ZipCPU/videozip/rtl/wbi2c/wbi2cslave.v

////////////////////////////////////////////////////////////////////////////////
//
// Filename:	rtl/wbi2c/wbi2cslave.v
// {{{
// Project:	VideoZip, a ZipCPU SoC supporting video functionality
//
// Purpose:	To create an I2C Slave that can be accessed via a wishbone bus.
//
//	This core works by creating a dual-port 128-byte memory, that can be
//	written to via either 1) the I2C bus which it acts as a slave upon,
//	2) an AXI slave port, or 3) the wishbone bus it is connected to.  The
//	128 bytes of slave memory may be referenced, read, and written to via
//	either of the I2C or WB busses.
//
//	The AXI slave port was added as an after thought to allow forwarding
//	of a read only I2C port (such as EDID info from a downstream monitor).
//
// Creator:	Dan Gisselquist, Ph.D.
//		Gisselquist Technology, LLC
//
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
// This program is distributed in the hope that it will be useful, but WITHOUT
// ANY WARRANTY; without even the implied warranty of MERCHANTIBILITY or
// FITNESS FOR A PARTICULAR PURPOSE.  See the GNU General Public License
// for more details.
//
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
////////////////////////////////////////////////////////////////////////////////
//
`default_nettype	none
// }}}
module	wbi2cslave #(
		// {{{
		// Verilator lint_off UNUSED
		parameter	INITIAL_MEM = "",
		// Verilator lint_on  UNUSED
		parameter [0:0]	WB_READ_ONLY  = 1'b0,
		parameter [0:0]	I2C_READ_ONLY = 1'b0,
		parameter [0:0]	AXIS_SUPPORT  = 1'b1,
		parameter [6:0]	SLAVE_ADDRESS = 7'h50,
		parameter	MEM_ADDR_BITS = 8
		// }}}
	) (
		// {{{
		input	wire		i_clk, i_reset,
		// Bus access
		// {{{
		input	wire		i_wb_cyc, i_wb_stb, i_wb_we,
		input	wire	[(MEM_ADDR_BITS-3):0]	i_wb_addr,
		input	wire	[31:0]	i_wb_data,
		input	wire	[3:0]	i_wb_sel,
		output	wire		o_wb_stall,
		output	reg		o_wb_ack,
		output	reg	[31:0]	o_wb_data,
		// }}}
		// AXI Stream access, for data from I2C
		// {{{
		input	wire		s_valid,
		output	wire		s_ready,
		input	wire	[7:0]	s_data,
		input	wire		s_last,
		// }}}
		// Actual I2C interaction
		// {{{
		input	wire		i_i2c_scl, i_i2c_sda,
		output	reg		o_i2c_scl, o_i2c_sda,
		// }}}
		output	wire	[31:0]	o_dbg
		// }}}
	);

	// Local declarations
	// {{{
	localparam [0:0] READ_ONLY = WB_READ_ONLY && I2C_READ_ONLY
							&& !AXIS_SUPPORT;

	localparam [2:0]	I2CIDLE	 = 3'h0,
				I2CSTART = 3'h1,
				I2CADDR	 = 3'h2,
				I2CSACK	 = 3'h3,// Slave ack's (that's us),
				I2CRX	 = 3'h4,// Slave receive's (that's us)
				I2CMACK	 = 3'h5,// Master acks's
				I2CTX	 = 3'h6,// Slave transmits
				I2CILLEGAL= 3'h7;

	localparam	[1:0]	BUS_IDLE = 2'b00,
				BUS_READ = 2'b01,
				BUS_SEND = 2'b10;

	reg	[31:0]	mem	[0:((1<<(MEM_ADDR_BITS-2))-1)];
	reg	[4:0]	wr_stb;
	reg	[7:0]	i2c_addr;
	wire	[7:0]	wr_data;

	reg	[3:0]	r_we;
	reg	[31:0]	r_data;
	reg	[(MEM_ADDR_BITS-3):0]	r_addr;

	reg	[(2*PL-1):0]	i2c_pipe;
	reg	last_scl, last_sda;
	// Current values are at the edge of the synchronizer
	wire	this_scl   = i2c_pipe[(2*PL-1)];
	wire	this_sda   = i2c_pipe[(2*PL-2)];

	// This allows us to notice edges
	wire	i2c_posedge= (!last_scl)&&( this_scl);
	wire	i2c_negedge= ( last_scl)&&(!this_scl);
	wire	i2c_start  = ( last_scl)&&( this_scl)&&( last_sda)&&(!this_sda);
	wire	i2c_stop   = ( last_scl)&&( this_scl)&&(!last_sda)&&( this_sda);

	reg	[2:0]	i2c_state;
	reg	[7:0]	dreg, oreg, rd_val, i2c_rx_byte;
	wire	[7:0]	i2c_tx_byte;
	reg	[2:0]	dbits;
	reg		slave_tx_rx_n, i2c_slave_ack, i2c_rx_stb, i2c_tx_stb;

	reg	[1:0]	bus_state;
	reg		go_bus_idle, wr_complete,
			bus_rd_stb, bus_wr_stb;
	reg	[2:0]	wr_pipe;
	reg	[31:0]	pipe_mem;
	reg	[1:0]	pipe_sel;
	reg	r_trigger;

	wire	[MEM_ADDR_BITS-1:0]	axis_addr;
	//

`ifndef	VERILATOR
	initial begin
		if (INITIAL_MEM != "")
			$readmemh(INITIAL_MEM, mem);
	end
`endif
	// }}}
	////////////////////////////////////////////////////////////////////////
	//
	// Wishbone interactions: Read/write set memory
	// {{{
	////////////////////////////////////////////////////////////////////////
	//
	//

	// r_data, r_addr, r_we
	// {{{
	initial	r_we = 4'h0;
	always @(posedge i_clk)
	begin
		if (!READ_ONLY)
		begin
			// Accept new data from one of three sources:
			//  1. An I2C write from the I2C master
			//	(Assuming the device can be adjusted via I2C)
			//  2. A write from the AXI stream slave port
			//  3. A WB write
			//	(Assuming the device can be adjusted via WB)
			// Writes require two clocks: one for the arbitration
			// below, and a second one to actually write the data
			// to memory.
			if ((!I2C_READ_ONLY)&&(wr_stb[4]))
			begin
				r_we <= wr_stb[3:0];
				r_addr <= i2c_addr[MEM_ADDR_BITS-1:2];
				r_data <= {(4){wr_data}};
			end else if (AXIS_SUPPORT && s_valid)
			begin
				r_we <= { 2'b00, axis_addr[1:0] };
				r_addr <= axis_addr[MEM_ADDR_BITS-1:2];
				r_data <= {(4){s_data}};
			end else if ((!WB_READ_ONLY)&&(i_wb_stb)&&(i_wb_we))
			begin
				r_we <= i_wb_sel;
				r_addr <= i_wb_addr;
				r_data <= i_wb_data;
			end
		end else
			r_we <= 4'h0;

		if (i_reset)
			r_we <= 4'h0;
	end
	// }}}

	// o_wb_data: Read from memory
	// {{{
	always @(posedge i_clk)
		o_wb_data <= mem[ i_wb_addr[(MEM_ADDR_BITS-3):0] ];
	// }}}

	// o_wb_ack, o_wb_stall
	// {{{
	initial	o_wb_ack = 1'b0;
	always @(posedge i_clk)
		o_wb_ack <= (i_wb_stb)&&(!o_wb_stall);

	// Stall on any write, when another source is also attempting to write
	//   to memory at the same time.
	assign	o_wb_stall = i_wb_we && ((!I2C_READ_ONLY && wr_stb[4])
						|| (AXIS_SUPPORT && s_valid));
	// }}}
	// }}}
	////////////////////////////////////////////////////////////////////////
	//
	// AXI Stream incoming data
	// {{{
	////////////////////////////////////////////////////////////////////////
	//
	//

	// AXI stream data can be used to set the memory of this I2C slave.
	// Writes will set one byte of memory at a time, and writes with TLAST
	// set will reset the address back to the beginning.

	generate if (AXIS_SUPPORT)
	begin : GEN_AXIS_ADDR
		reg	[MEM_ADDR_BITS-1:0]	r_axis_addr;

		initial	r_axis_addr = 0;
		always @(posedge i_clk)
		if (i_reset)
			r_axis_addr <= 0;
		else if (s_valid && s_ready)
		begin
			if (s_last)
				r_axis_addr <= 0;
			else
				r_axis_addr <= axis_addr + 1;
		end

		assign	axis_addr = r_axis_addr;

	end else begin : NO_AXIS_ADDR_SUPPORT
		assign	axis_addr = 0;
	end endgenerate

	assign	s_ready = (!AXIS_SUPPORT || I2C_READ_ONLY || !wr_stb[4]);

	// }}}
	////////////////////////////////////////////////////////////////////////
	//
	// Write to memory
	// {{{
	always @(posedge i_clk)
	if (!READ_ONLY)
	begin
		if (r_we[3])
			mem[r_addr][31:24] <= r_data[31:24];
		if (r_we[2])
			mem[r_addr][23:16] <= r_data[23:16];
		if (r_we[1])
			mem[r_addr][15: 8] <= r_data[15: 8];
		if (r_we[0])
			mem[r_addr][ 7: 0] <= r_data[ 7: 0];
	end
	// }}}
	////////////////////////////////////////////////////////////////////////
	//
	// I2C Controller
	// {{{
	////////////////////////////////////////////////////////////////////////
	//
	//


	//
	//
	// Okay, that builds our memory, and gives us access to the bus.
	// Now ... let's build the I2C slave portion to interact over that bus
	//
	//

	// 2FF Synchronizer
	localparam	PL=2;
	always @(posedge i_clk)
		i2c_pipe <= { i2c_pipe[(2*PL-3):0], i_i2c_scl, i_i2c_sda };

	// Capture the last values
	always @(posedge i_clk)
	begin
		last_scl <= i2c_pipe[(2*PL-1)];
		last_sda <= i2c_pipe[(2*PL-2)];
	end

	// i2c_state, o_i2c_scl, o_i2c_sda, i2c_slave_ack, i2c_*x_stb,dreg,oreg
	// {{{
	initial	i2c_state = I2CIDLE;
	initial	o_i2c_scl = 1'b1;
	initial	o_i2c_sda = 1'b1;
	initial	i2c_slave_ack  = 1'b1;
	always	@(posedge i_clk)
	begin
		// Default is to do nothing with the output ports.  A 1'b1 does
		// that.
		o_i2c_scl <= 1'b1;
		o_i2c_sda <= 1'b1;
		i2c_tx_stb <= 1'b0;
		i2c_rx_stb <= 1'b0;
		if (i2c_posedge)
			dreg  <= { dreg[6:0], this_sda };
		if (i2c_negedge)
			oreg  <= { oreg[6:0], oreg[0] };
		case(i2c_state)
		I2CIDLE: begin
			// {{{
			dbits <= 0;
			if (i2c_start)
				i2c_state <= I2CSTART;
			end
			// }}}
		I2CSTART: begin
			// {{{
				dbits <= 0;
				if (i2c_negedge)
					i2c_state <= I2CADDR;
			end
			// }}}
		I2CADDR: begin
			// {{{
				if (i2c_negedge)
					dbits <= dbits + 1'b1;
				if ((i2c_negedge)&&(dbits == 3'h7))
				begin
					slave_tx_rx_n <= dreg[0];
					if (dreg[7:1] == SLAVE_ADDRESS)
					begin
						i2c_state <= I2CSACK;
						i2c_slave_ack <= 1'b0;
					end else begin
						// Ignore this, its not for
						// me.
						i2c_state <= I2CILLEGAL;
						i2c_slave_ack <= 1'b1;
					end
				end
			end
			// }}}
		I2CSACK: begin
			// {{{
				dbits <= 3'h0;
				// NACK anything outside of our address range
				o_i2c_sda <= i2c_slave_ack;
				oreg <= rd_val;
				if (i2c_negedge)
				begin
					i2c_state <= (slave_tx_rx_n)? I2CTX:I2CRX;
					oreg <= i2c_tx_byte;
				end
			end
			// }}}
		I2CRX: begin	// Slave reads from the bus
			// {{{
				//
				// First byte received is always the memory
				// address.
				//
				if (i2c_negedge)
					dbits <= dbits + 1'b1;
				if ((i2c_negedge)&&(dbits == 3'h7))
				begin
					i2c_rx_byte <= dreg;
					i2c_rx_stb  <= 1'b1;
					i2c_state <= I2CSACK;
				end
			end
			// }}}
		I2CTX: begin	// Slave transmits
			// {{{
				// Read from the slave (that's us)
				if (i2c_negedge)
					dbits <= dbits + 1'b1;
				if ((i2c_negedge)&&(dbits == 3'h7))
				begin
					i2c_tx_stb <= 1'b1;
					i2c_state <= I2CMACK;
				end
				o_i2c_sda <= oreg[7];
			end
			// }}}
		I2CMACK: begin
			// {{{
				dbits <= 3'h0;
				if (i2c_negedge)
				begin
					i2c_state <= I2CTX;
					oreg <= i2c_tx_byte;
				end
				oreg <= rd_val;
			end
			// }}}
		I2CILLEGAL:	dbits <= 3'h0;
		// default:	dbits <= 3'h0;
		endcase
		if (i2c_stop)
			i2c_state <= I2CIDLE;
		else if (i2c_start)
			i2c_state <= I2CSTART;
	end
	// }}}

	// bus_*_stb, wr_complete, go_bus_idle, bus_state
	// {{{
	initial		wr_complete = 1'b0;
	initial		bus_rd_stb  = 1'b0;
	initial		bus_wr_stb  = 1'b0;
	initial		bus_state   = BUS_IDLE;
	initial		go_bus_idle = 1'b0;
	always @(posedge i_clk)
	begin
		go_bus_idle <= ((i2c_state == I2CIDLE)
				||(i2c_state == I2CSTART)
				||(i2c_state == I2CILLEGAL));
		bus_rd_stb <= 1'b0;
		bus_wr_stb <= 1'b0;
		if (go_bus_idle)
			bus_state <= BUS_IDLE;
		else case(bus_state)
		BUS_IDLE: begin
			// {{{
			if (i2c_rx_stb)
			begin
				i2c_addr <= i2c_rx_byte;
				bus_state <= BUS_READ;
				bus_rd_stb <= 1'b1;
			end else if (i2c_tx_stb)
			begin
				bus_state <= BUS_SEND;
				i2c_addr <= i2c_addr + 1'b1;
				bus_rd_stb <= 1'b1;
			end end
			// }}}
		BUS_READ: if (i2c_rx_stb)
			// {{{
			begin
				// Reading from the bus means we are
				// writing to memory
				bus_wr_stb <= (!I2C_READ_ONLY);
			end
			// Increment the address once a write completes
			// }}}
		BUS_SEND: if (i2c_tx_stb)
			// {{{
			begin
				// Once we've finished transmitting,
				// increment the address to read the
				// next item
				i2c_addr <= i2c_addr + 1'b1;
				bus_rd_stb <= 1'b1;
			end
			// }}}
		default: begin end
		endcase

		if (wr_complete)
		begin
			i2c_addr <= i2c_addr + 1'b1;
			bus_rd_stb <= 1'b1;
		end
	end
	// }}}

	// wr_pipe, wr_complete
	// {{{
	initial	wr_pipe     = 3'h0;
	initial	wr_complete = 1'b0;
	always @(posedge i_clk)
		wr_pipe <= { wr_pipe[1:0], bus_wr_stb };
	always @(posedge i_clk)
		wr_complete <= wr_pipe[2];
	// }}}

	// wr_stb
	// {{{
	initial	wr_stb = 5'b0;
	always @(posedge i_clk)
	if (!I2C_READ_ONLY)
	begin
		wr_stb[4]  <= bus_wr_stb;
		wr_stb[3]  <= (bus_wr_stb)&&(i2c_addr[1:0]==2'b00);
		wr_stb[2]  <= (bus_wr_stb)&&(i2c_addr[1:0]==2'b01);
		wr_stb[1]  <= (bus_wr_stb)&&(i2c_addr[1:0]==2'b10);
		wr_stb[0]  <= (bus_wr_stb)&&(i2c_addr[1:0]==2'b11);
	end
	// }}}

	assign	wr_data = i2c_rx_byte;


	// Read from memory
	// {{{
	always @(posedge i_clk)
	if(bus_rd_stb)
		pipe_mem <= mem[i2c_addr[(MEM_ADDR_BITS-1):2]];
	// }}}

	// pipe_sel
	// {{{
	always @(posedge i_clk)
	if (bus_rd_stb)
		pipe_sel <= i2c_addr[1:0];
	// }}}

	// rd_val
	// {{{
	always @(posedge i_clk)
	case(pipe_sel)
	2'b00: rd_val <= pipe_mem[31:24];
	2'b01: rd_val <= pipe_mem[23:16];
	2'b10: rd_val <= pipe_mem[15: 8];
	2'b11: rd_val <= pipe_mem[ 7: 0];
	endcase
	// }}}

	assign	i2c_tx_byte = rd_val;
	// }}}
	// Debug port
	// {{{
	initial	r_trigger = 1'b0;
	always @(posedge i_clk)
		r_trigger <= i2c_start;

	assign	o_dbg = { r_trigger, 3'h0,
			i_wb_stb, i_wb_we && i_wb_stb, o_wb_stall,
					o_wb_ack, 2'b00,i_wb_addr[5:0],	// 12b
			s_valid, s_ready, s_last, 1'b0, s_data,		// 12b
			i_i2c_scl, i_i2c_sda, o_i2c_scl, o_i2c_sda	//  4b
			};
	// }}}

	// Make verilator happy
	// {{{
	// verilator lint_off UNUSED
	wire	[1:0]	unused;
	assign	unused = { i_wb_cyc, i_reset };
	// verilator lint_on  UNUSED
	// }}}
////////////////////////////////////////////////////////////////////////////////
////////////////////////////////////////////////////////////////////////////////
////////////////////////////////////////////////////////////////////////////////
//
// Formal properties
// {{{
////////////////////////////////////////////////////////////////////////////////
////////////////////////////////////////////////////////////////////////////////
////////////////////////////////////////////////////////////////////////////////
`ifdef	FORMAL
`endif
// }}}
endmodule
