ZipCPU/videozip/rtl/sdspi/sdcmd.v

////////////////////////////////////////////////////////////////////////////////
//
// Filename:	rtl/sdspi/sdcmd.v
// {{{
// Project:	VideoZip, a ZipCPU SoC supporting video functionality
//
// Purpose:	Bi-directional command line processor.  This generates the
//		command line inputs to the PHY, and receives its outputs.
//	Commands are requested from the CPU, and responses gathered and
//	returned to the register set.
//
// Creator:	Dan Gisselquist, Ph.D.
//		Gisselquist Technology, LLC
//
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
// This program is distributed in the hope that it will be useful, but WITHOUT
// ANY WARRANTY; without even the implied warranty of MERCHANTIBILITY or
// FITNESS FOR A PARTICULAR PURPOSE.  See the GNU General Public License
// for more details.
//
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
////////////////////////////////////////////////////////////////////////////////
//
`timescale	1ns/1ps
`default_nettype	none
// }}}
module	sdcmd #(
		// {{{
		// parameter	MW = 32,
		// parameter [0:0]	OPT_LITTLE_ENDIAN = 1'b0,
		parameter [0:0]	OPT_EMMC = 1'b1,
		parameter [0:0]	OPT_DS = (OPT_EMMC),
		parameter	LGTIMEOUT = 26,	// 500ms expected
		parameter	LGLEN = 9,
		parameter	MW = 32
		// }}}
	) (
		// {{{
		input	wire			i_clk, i_reset,
		// Configuration bits
		input	wire			i_cfg_ds,	// Use ASYNC
		input	wire			i_cfg_dbl,	// 2Bits/Clk
		input	wire			i_ckstb,
		// Controller interface
		// {{{
		input	wire			i_cmd_request,
		input	wire			i_cmd_selfreply,
		input	wire	[1:0]		i_cmd_type,
		input	wire	[6:0]		i_cmd,
		input	wire	[31:0]		i_arg,

		output	wire			o_busy,
		output	reg			o_done,
		output	reg			o_err,
		output	reg	[1:0]		o_ercode,
		// }}}
		// Send to the front end
		// {{{
		output	wire			o_cmd_en,
		// output	wire		o_pp_cmd,	// From CFG reg
		output	wire	[1:0]		o_cmd_data,
		// }}}
		// Receive from the front end
		// {{{
		input	wire	[1:0]		i_cmd_strb,
		input	wire	[1:0]		i_cmd_data,
		input	wire			i_cmd_collision,
		// input	wire		i_dat_busy,

		input	wire			S_ASYNC_VALID,
		input	wire	[1:0]		S_ASYNC_DATA,
		// }}}
		// Return the result
		output	reg			o_cmd_response,
		output	reg	[5:0]		o_resp,
		output	reg	[31:0]		o_arg,
		// Writes to memory
		// {{{
		output	reg			o_mem_valid,
		output	wire	[MW/8-1:0]	o_mem_strb,
		output	wire	[LGLEN-1:0]	o_mem_addr,	// Word address
		output	reg	[MW-1:0]	o_mem_data	// Outgoing data
		// }}}
		// }}}
	);

	// Local declarations
	// {{{
	localparam [1:0]	R_NONE = 2'b00,
				R_R1   = 2'b01,
				R_R2   = 2'b10;
				// R_R1b  = 2'b11;

	localparam [1:0]	ECODE_TIMEOUT = 2'b00,
				ECODE_OKAY    = 2'b01,
				ECODE_BADCRC  = 2'b10,
				ECODE_FRAMEERR= 2'b11;

	localparam	[6:0]	CRC_POLYNOMIAL = 7'h09;

	reg		active;
	reg	[5:0]	srcount;
	reg	[47:0]	tx_sreg;

	reg		waiting_on_response, cfg_ds, cfg_dbl, r_frame_err,
			response_active;
	wire		self_request;
	wire		lcl_accept;
	reg	[1:0]	cmd_type;
	reg	[7:0]	resp_count;
	wire		frame_err, w_done, crc_err, w_no_response;
	reg	[LGLEN+$clog2(MW/32)-1:0]	mem_addr;
	reg	[39:0]	rx_sreg;

	reg			rx_timeout;
	wire			no_timeout;
	reg	[LGTIMEOUT-1:0]	rx_timeout_counter;

	reg	[6:0]	crc_fill;
	reg		r_busy, new_data;

	reg		r_delay;
	reg	[3:0]	r_dly_count;

	reg		r_done;

	// }}}
	////////////////////////////////////////////////////////////////////////
	//
	// Send 48b command to card
	// {{{
	////////////////////////////////////////////////////////////////////////
	//
	//

	initial { active, srcount } = 0;
	always @(posedge i_clk)
	if (i_reset)
	begin
		active <= 0;
		srcount <= 0;
	end else if (OPT_EMMC && active && i_cmd_collision)
	begin
		// This will only happen on an IRQ return
		active  <= 0;
		srcount <= 0;
	end else if (lcl_accept)
	begin
		srcount <= 48;
		active  <= 1;
		// sreg <= { i_cmd, i_arg, CMDCRC({ i_cmd, i_arg }), 1'b1 };
	end else if (i_ckstb && srcount != 0)
	begin
		if (cfg_dbl)
		begin
			// sreg <= { sreg[45:0], 2'b11 };
			active <= (srcount > 2);
			srcount <= srcount - 2;
		end else begin
			// sreg <= { sreg[46:0], 2'b1 };
			active <= (srcount > 1);
			srcount <= srcount - 1;
		end
	end
	
	always @(posedge i_clk)
	if (i_reset)
		tx_sreg <= 48'hffff_ffff_ffff;
	else if (OPT_EMMC && active && i_cmd_collision)
	begin
		tx_sreg <= 48'hffff_ffff_ffff;
	end else if (lcl_accept)
		tx_sreg <= { 1'b0, i_cmd, i_arg,
				CMDCRC({ 1'b0, i_cmd, i_arg }), 1'b1 };
	else if (i_ckstb)
	begin
		if (cfg_dbl)
			tx_sreg <= { tx_sreg[45:0], 2'b11 };
		else
			tx_sreg <= { tx_sreg[46:0], 1'b1 };
	end

	assign	o_cmd_en = active;
	assign	o_cmd_data = (cfg_dbl) ? tx_sreg[47:46] : {(2){tx_sreg[47]}};

	// }}}
	////////////////////////////////////////////////////////////////////////
	//
	// Receive response from card
	// {{{
	////////////////////////////////////////////////////////////////////////
	//
	//

	// waiting_on_response
	// {{{
	initial	waiting_on_response = 1'b0;
	always @(posedge i_clk)
	if (i_reset)
		waiting_on_response <= 1'b0;
	else if (lcl_accept)
		waiting_on_response <= (i_cmd_type != R_NONE);
	else if (o_done)
		waiting_on_response <= 1'b0;
	// }}}

	// cfg_ds, cfg_dbl, cmd_type
	// {{{
	always @(posedge i_clk)
	if (i_reset)
		{ cfg_ds, cfg_dbl, cmd_type } <= 4'b0;
	else if (lcl_accept)
		{ cfg_ds, cfg_dbl, cmd_type } <= { (i_cfg_ds && OPT_DS), i_cfg_dbl, i_cmd_type };
	// }}}

	// new_data
	// {{{
	always @(posedge i_clk)
	if (i_reset || !waiting_on_response || active)
		new_data <= 0;
	else if (OPT_DS && cfg_ds)
		new_data <= S_ASYNC_VALID;
	else
		new_data <= |i_cmd_strb;
	// }}}
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
